zxchurka1488/vfs2_electronic_predprof/Фотографии/photo_6_2025-02-09_21-51-31.jpg

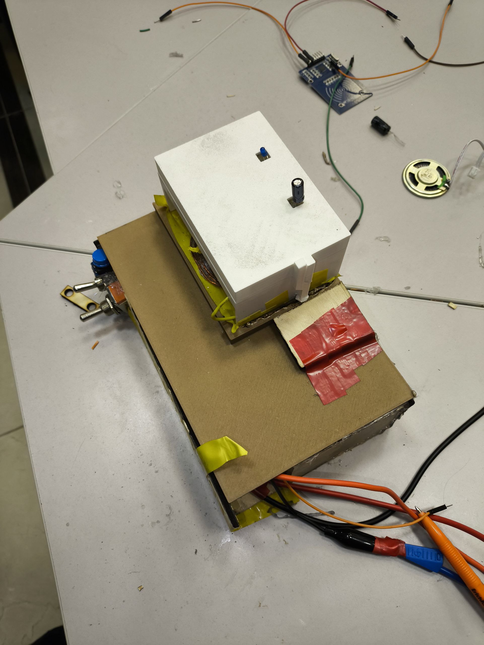
Фотографии/photo_6_2025-02-09_21-51-31.jpg
